YePererva/type_c_adapter/references/bracket_drawings/usb-c.jpg

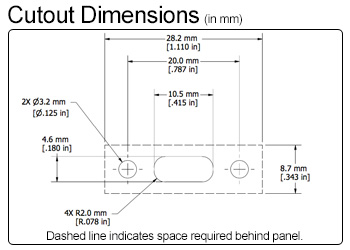
references/bracket_drawings/usb-c.jpg
